Neofoxx/Livolo-RF-stick/08_Livolofier/inc/peripherals/LED.h

#ifndef LED_H_1bbf1140eed64c8eb493ff52fbe25fc3
#define LED_H_1bbf1140eed64c8eb493ff52fbe25fc3

void LED_init();
void LED_setGreen(uint8_t setState);
void LED_setRed(uint8_t setState);
void LED_toggle();

#endif
